johnyHV/simpsonstv/docu/hw/final.jpg

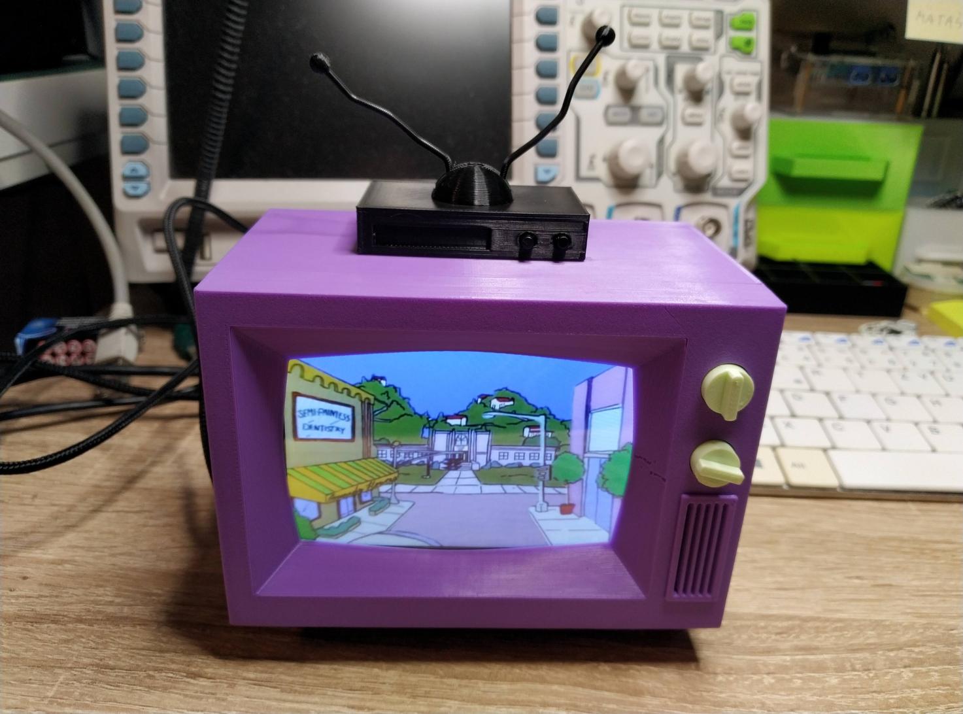
docu/hw/final.jpg
