johnyHV/simpsonstv/docu/HW_parts/raspberry-pi-zero.jpg

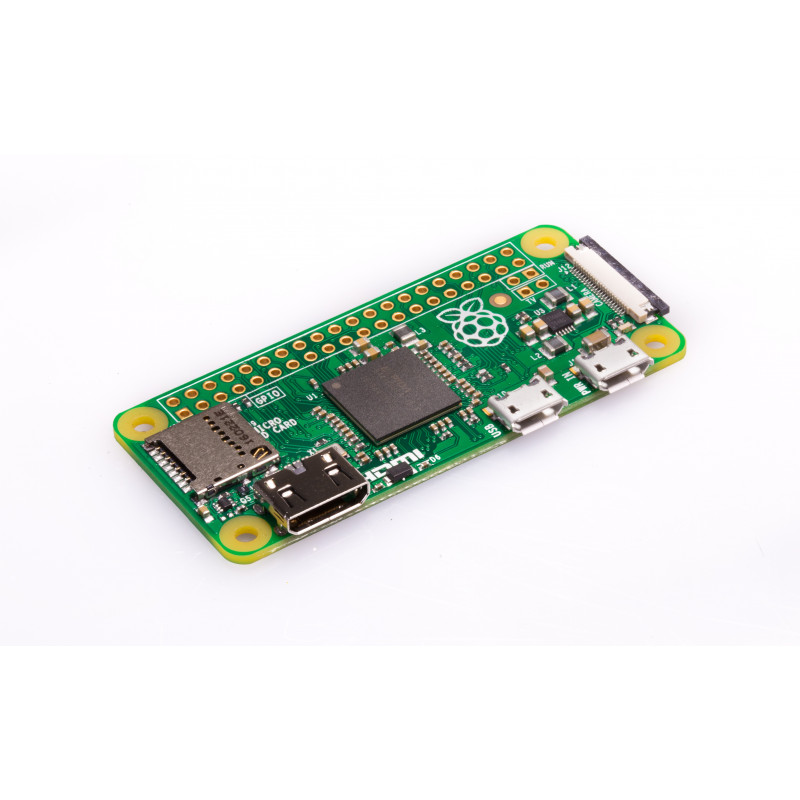
docu/HW_parts/raspberry-pi-zero.jpg
